TransFormInters/Tridibot/Tridibot_Quadruped_Arduino_and_ESP8266_Robot/images/414fe623fab630fe7a909ece4c7568c5.jpg

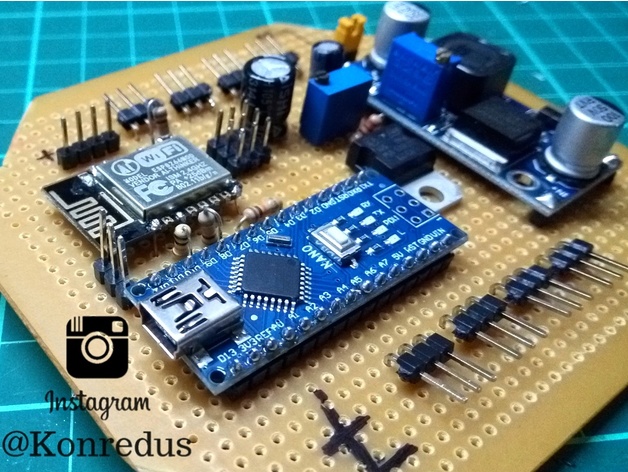
Tridibot_Quadruped_Arduino_and_ESP8266_Robot/images/414fe623fab630fe7a909ece4c7568c5.jpg
