TransFormInters/Tridibot/Tridibot_Quadruped_Arduino_and_ESP8266_Robot/images/91306b38b43a87959a78602864193e61.jpg

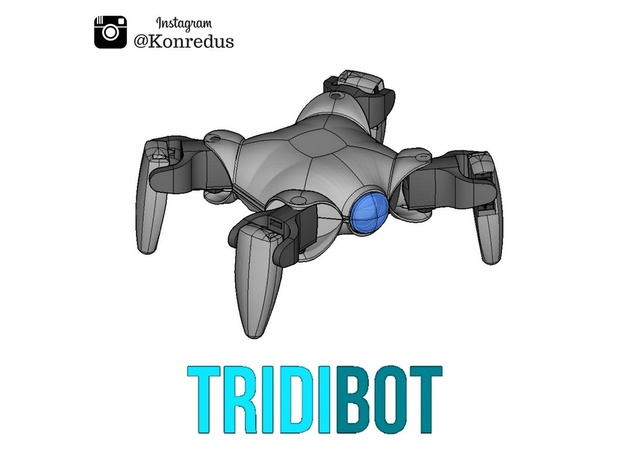
Tridibot_Quadruped_Arduino_and_ESP8266_Robot/images/91306b38b43a87959a78602864193e61.jpg
