TransFormInters/Tridibot/Tridibot_Quadruped_Arduino_and_ESP8266_Robot/images/538739f4376f88abbd34e0c300964b62.jpg

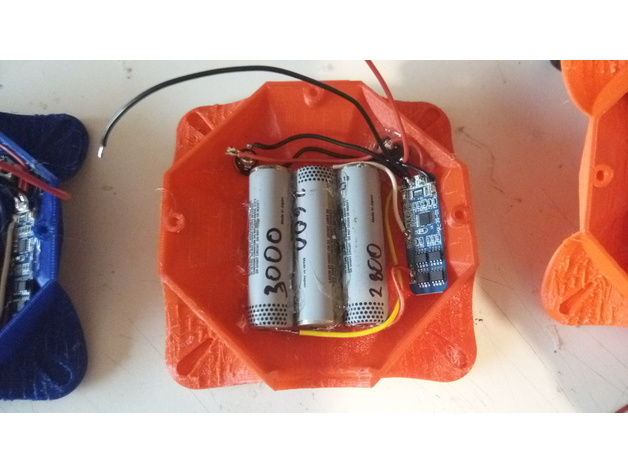
Tridibot_Quadruped_Arduino_and_ESP8266_Robot/images/538739f4376f88abbd34e0c300964b62.jpg
