TransFormInters/Tridibot/Tridibot_Quadruped_Arduino_and_ESP8266_Robot/images/Tridibot_leg.jpg

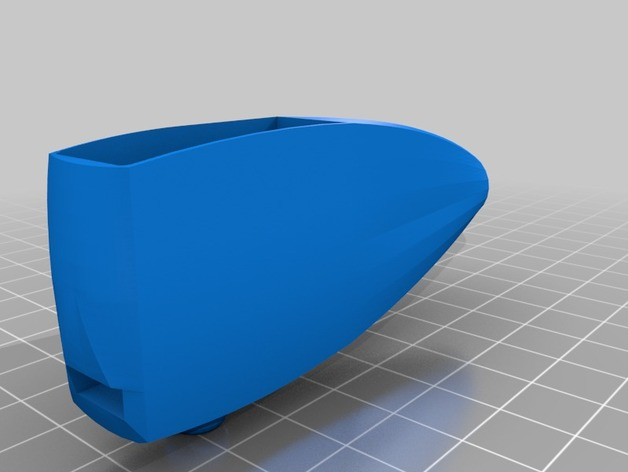
Tridibot_Quadruped_Arduino_and_ESP8266_Robot/images/Tridibot_leg.jpg
