TransFormInters/Tridibot/Tridibot_Quadruped_Arduino_and_ESP8266_Robot/images/Tridibot_servo_cover.jpg

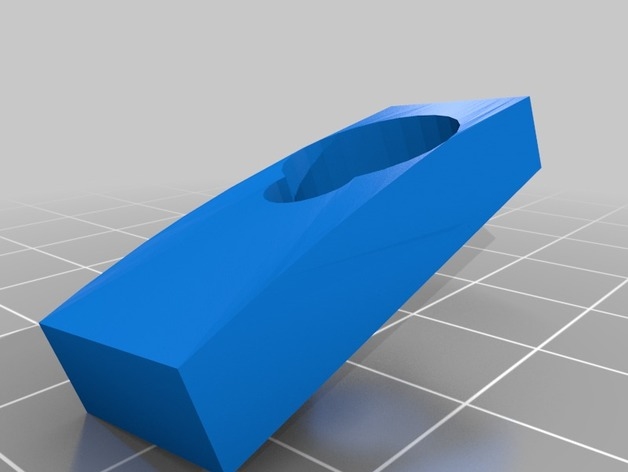
Tridibot_Quadruped_Arduino_and_ESP8266_Robot/images/Tridibot_servo_cover.jpg
